gjorando/ashpd/stl_files/finger_tip.stl

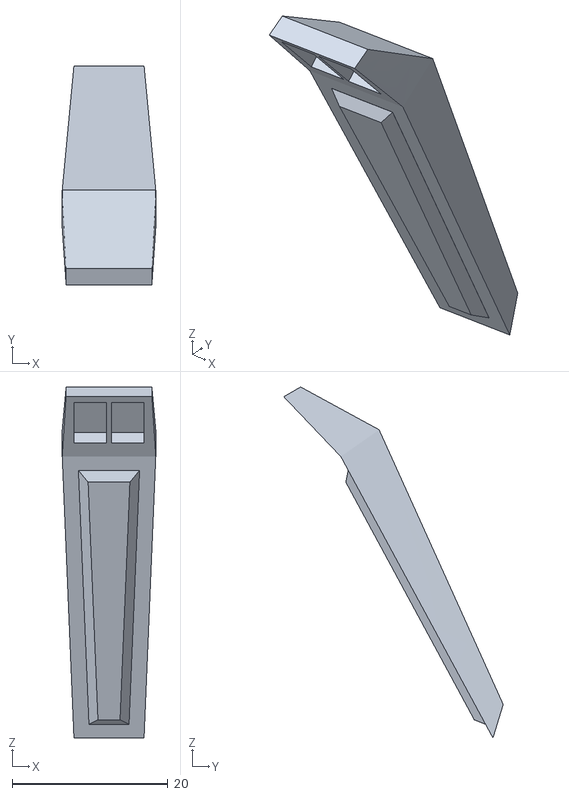
[picture p15: CAD file, 2023-01-16]
stl_files/finger_tip.stl
12.0 x 28.2 x 45.0
