gjorando/ashpd/stl_files/finger_base.stl

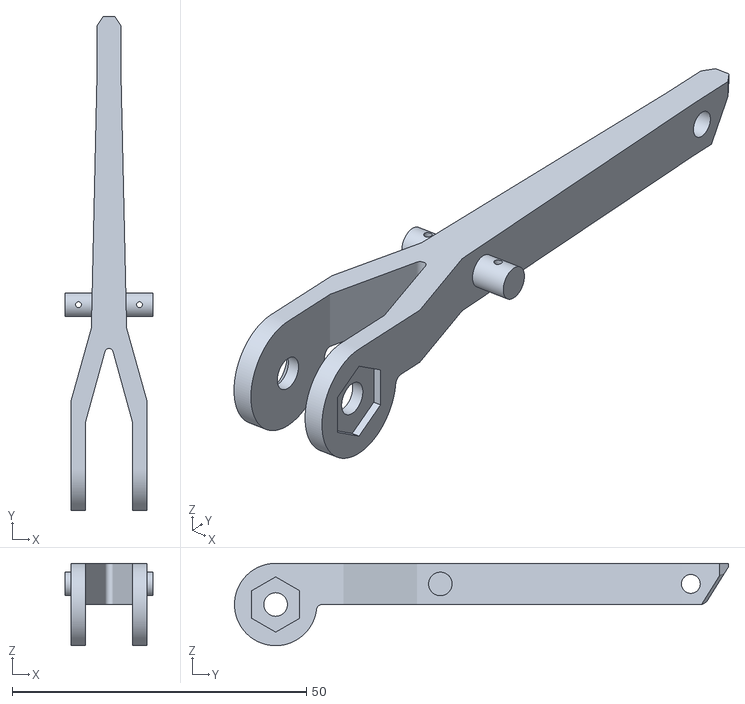
[picture p16: CAD file, 2023-01-16]
stl_files/finger_base.stl
15.0 x 84.0 x 14.0
