gjorando/ashpd/stl_files/finger_insert.stl

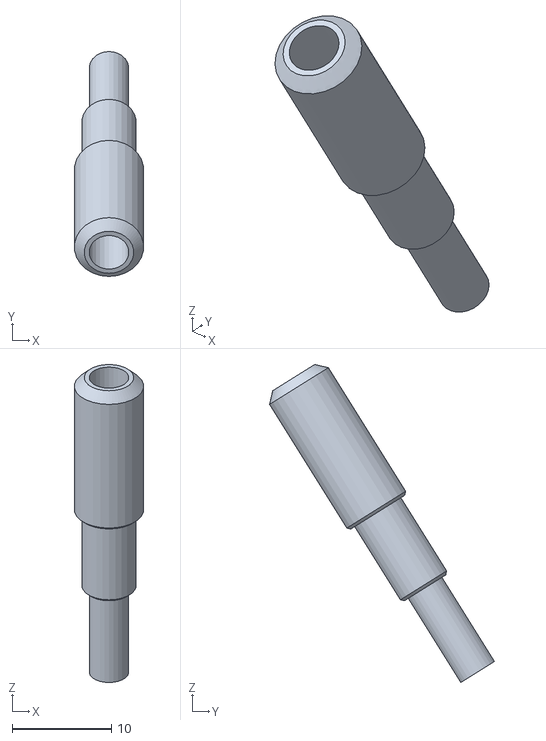
[picture p17: CAD file, 2023-01-16]
stl_files/finger_insert.stl
6.95 x 22.7 x 32.1
